eivindbohler/itxllama/kicad/3dmodels/5176139.step

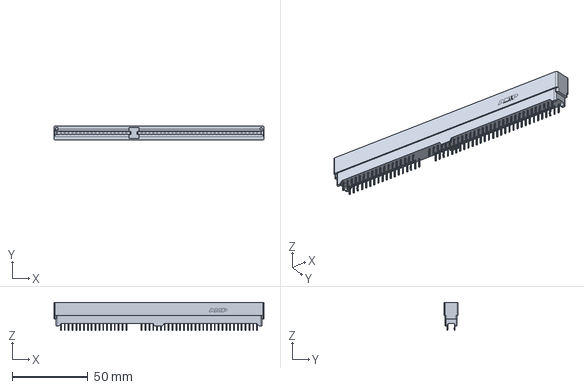
[picture p27: CAD file, 2024-02-07]
kicad/3dmodels/5176139.step
138.7 x 9.47 x 18.7 mm
