eivindbohler/itxllama/mechanical/fan_mount/fan_mount_nut.step

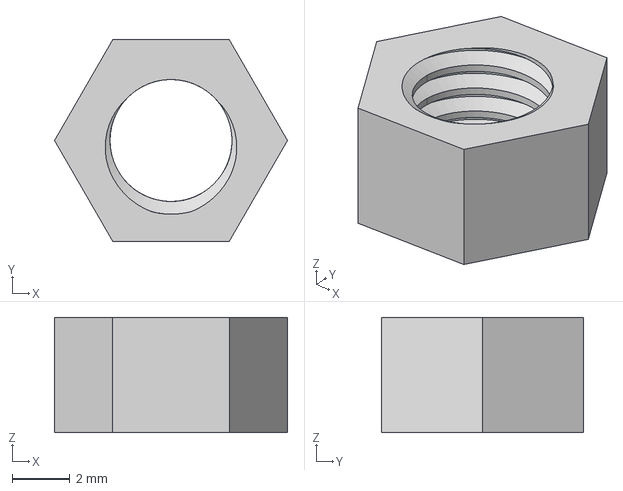
[picture p28: CAD file, 2023-12-06]
mechanical/fan_mount/fan_mount_nut.step
8.08 x 7.00 x 4.00 mm
