eivindbohler/itxllama/mechanical/fan_mount/fan_nut.step

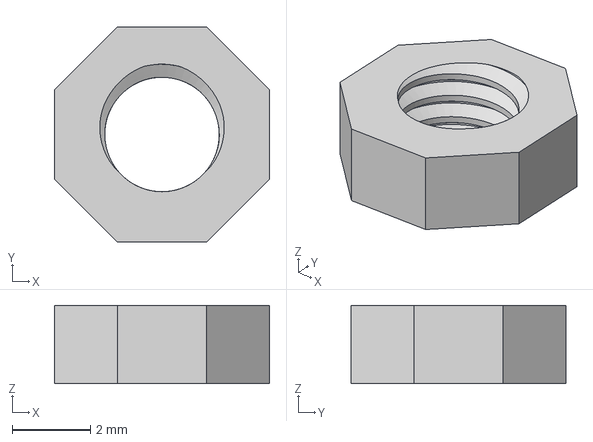
[picture p29: CAD file, 2023-12-06]
mechanical/fan_mount/fan_nut.step
5.50 x 5.50 x 2.00 mm
