eivindbohler/itxllama/kicad/3dmodels/JA33333-DA18-4F-combined.step

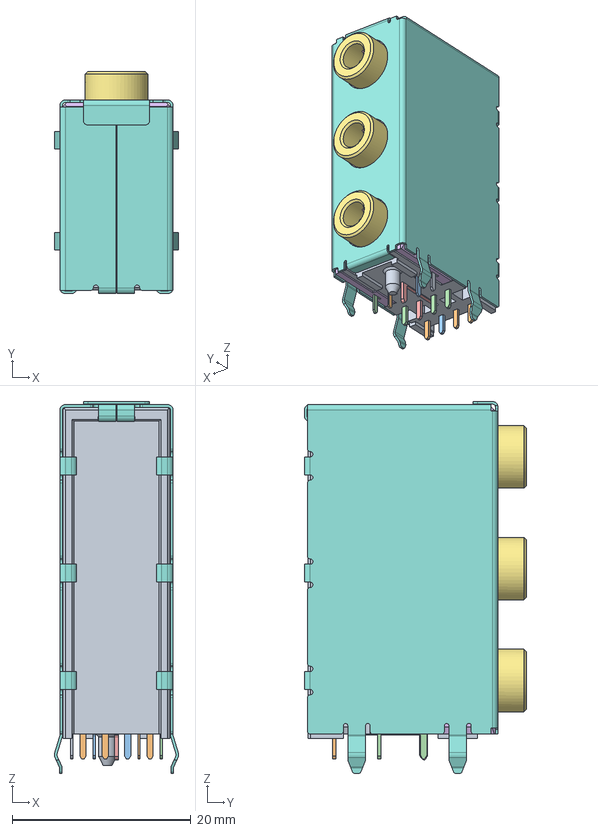
[picture p30: CAD file, 2024-02-07]
kicad/3dmodels/JA33333-DA18-4F-combined.step
13.9 x 24.9 x 41.6 mm
CONTACT2-X1
CONTAACT3-X5_
CONTACT4-X1
CONTACT5-X1
GROUNDINGCONTACT_____
HOUSINGX1__
RING___ (2) (1) x 3
SPACER1___
TAIL1_DOUBLEJACK
TAIL2_DOUBLEJACK
